SmokingDevices/CS2015/processing/ahrs-data/ahrs_data_display.pde

/******************************************************************************************
* Test Sketch for Razor AHRS v1.4.2
* 9 Degree of Measurement Attitude and Heading Reference System
* for Sparkfun "9DOF Razor IMU" and "9DOF Sensor Stick"
*
* Released under GNU GPL (General Public License) v3.0
* Copyright (C) 2013 Peter Bartz [http://ptrbrtz.net]
* Copyright (C) 2011-2012 Quality & Usability Lab, Deutsche Telekom Laboratories, TU Berlin
* Written by Peter Bartz (peter-bartz@gmx.de)
*
* Infos, updates, bug reports, contributions and feedback:
*     https://github.com/ptrbrtz/razor-9dof-ahrs
******************************************************************************************/

/*
  NOTE: There seems to be a bug with the serial library in Processing versions 1.5
  and 1.5.1: "WARNING: RXTX Version mismatch ...".
  Processing 2.0.x seems to work just fine. Later versions may too.
  Alternatively, the older version 1.2.1 also works and is still available on the web.
*/

import processing.opengl.*;

// IF THE SKETCH CRASHES OR HANGS ON STARTUP, MAKE SURE YOU ARE USING THE RIGHT SERIAL PORT:
// 1. Have a look at the Processing console output of this sketch.
// 2. Look for the serial port list and find the port you need (it's the same as in Arduino).
// 3. Set your port number here:
// final static int SERIAL_PORT_NUM = 0;
// 4. Try again.



float yaw = 0.0f;
float pitch = 0.0f;
float roll = 0.0f;
float yawOffset = 0.0f;

PFont font;

String[] lines;
int currPos = 0;


boolean synched = false;

void drawArrow(float headWidthFactor, float headLengthFactor) {
  float headWidth = headWidthFactor * 200.0f;
  float headLength = headLengthFactor * 200.0f;
  
  pushMatrix();
  
  // Draw base
  translate(0, 0, -100);
  box(100, 100, 200);
  
  // Draw pointer
  translate(-headWidth/2, -50, -100);
  beginShape(QUAD_STRIP);
    vertex(0, 0 ,0);
    vertex(0, 100, 0);
    vertex(headWidth, 0 ,0);
    vertex(headWidth, 100, 0);
    vertex(headWidth/2, 0, -headLength);
    vertex(headWidth/2, 100, -headLength);
    vertex(0, 0 ,0);
    vertex(0, 100, 0);
  endShape();
  beginShape(TRIANGLES);
    vertex(0, 0, 0);
    vertex(headWidth, 0, 0);
    vertex(headWidth/2, 0, -headLength);
    vertex(0, 100, 0);
    vertex(headWidth, 100, 0);
    vertex(headWidth/2, 100, -headLength);
  endShape();
  
  popMatrix();
}

void drawBoard() {
  pushMatrix();

  rotateY(-radians(yaw - yawOffset));
  rotateX(-radians(pitch));
  rotateZ(radians(roll)); 

  // Board body
  fill(255, 0, 0);
  box(250, 20, 400);
  
  // Forward-arrow
  pushMatrix();
  translate(0, 0, -200);
  scale(0.5f, 0.2f, 0.25f);
  fill(0, 255, 0);
  drawArrow(1.0f, 2.0f);
  popMatrix();
    
  popMatrix();
}

// Global setup
void setup() {
  // Setup graphics
  size(640, 480, OPENGL);
  smooth();
  noStroke();
  frameRate(50);
  
  // Load font
  font = loadFont("Univers-66.vlw");
  textFont(font);
  lines = loadStrings("/home/jklug/tools/10DOF.TXT");
  
  
}

/*
float readFloat(Serial s) {
  // Convert from little endian (Razor) to big endian (Java) and interpret as float
  return Float.intBitsToFloat(s.read() + (s.read() << 8) + (s.read() << 16) + (s.read() << 24));
}
*/

void draw() {
   // Reset scene
  background(0);
  lights();

  // Read angles from serial port
  if (currPos < lines.length) {
    float[] nums = float(split(lines[currPos], ','));
    yaw = nums[12];//aw + 0.1f; //readFloat(serial);
    pitch = nums[11];//pitch + 0.1f; //readFloat(serial);
    roll = nums[10];//roll + 0.1f; //readFloat(serial);
    /*
    yaw = yaw + 0.1f; //readFloat(serial);
    pitch = pitch + 0.1f; //readFloat(serial);
    roll = roll + 0.1f; //readFloat(serial);
    */
    
    currPos++;
  }
  if (currPos > lines.length) {
    currPos = 0;
  }

  // Draw board
  pushMatrix();
  translate(width/2, height/2, -350);
  drawBoard();
  popMatrix();
  
  textFont(font, 20);
  fill(255);
  textAlign(LEFT);

  // Output info text
  //text("Point FTDI connector towards screen and press 'a' to align", 10, 25);

  // Output angles
  pushMatrix();
  translate(10, height - 10);
  textAlign(LEFT);
  text("Yaw: " + ((int) yaw), 0, 0);
  text("Pitch: " + ((int) pitch), 150, 0);
  text("Roll: " + ((int) roll), 300, 0);
  text("Line: " + ((int) currPos) +"/"+ ((int) lines.length), 450, 0);
  popMatrix();
  delay(100);
}

void keyPressed() {
  /*
  switch (key) {
    case '0':  // Turn Razor's continuous output stream off
      serial.write("#o0");
      break;
    case '1':  // Turn Razor's continuous output stream on
      serial.write("#o1");
      break;
    case 'f':  // Request one single yaw/pitch/roll frame from Razor (use when continuous streaming is off)
      serial.write("#f");
      break;
    case 'a':  // Align screen with Razor
      yawOffset = yaw;
  }
  */
}
